CastaliaInstitute/luminary/assets/display-nubble-720x1280.png

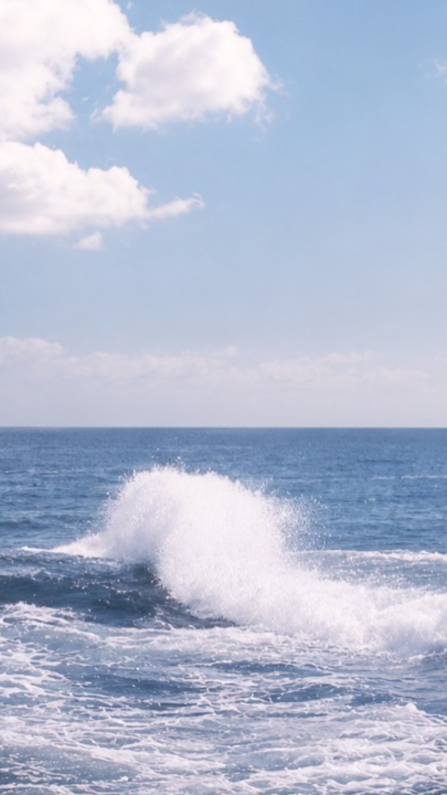
assets/display-nubble-720x1280.png
