CastaliaInstitute/luminary/assets/display-nubble-1024x600.png

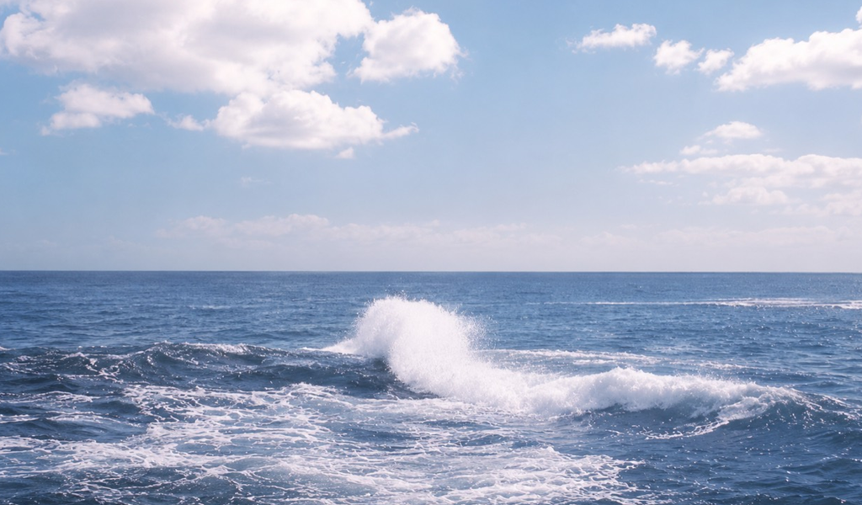
assets/display-nubble-1024x600.png
