CastaliaInstitute/luminary/assets/display-nubble-1131x720.png

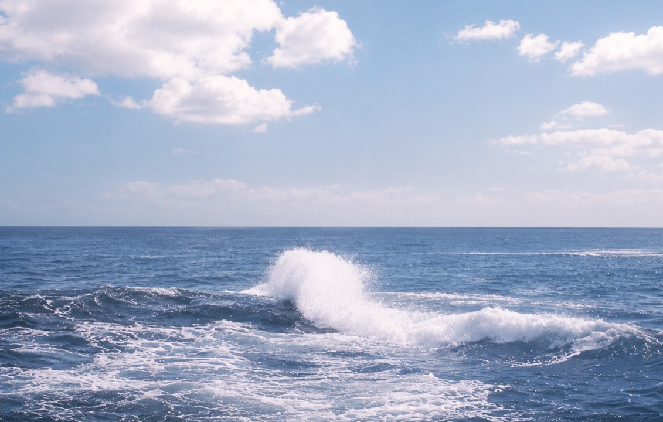
assets/display-nubble-1131x720.png
