CastaliaInstitute/luminary/assets/display-sky-sea-1280x720.png

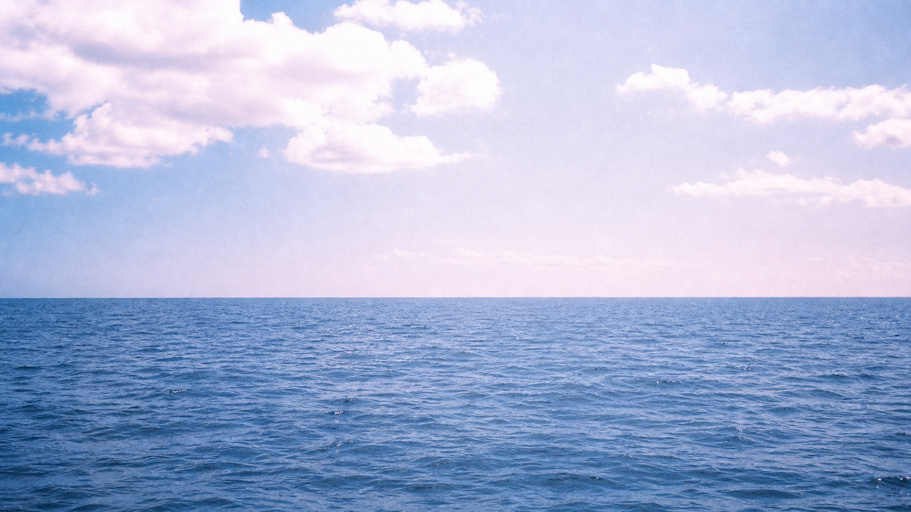
assets/display-sky-sea-1280x720.png
