CastaliaInstitute/luminary/assets/lighthouse-silhouette-reference-v2.png

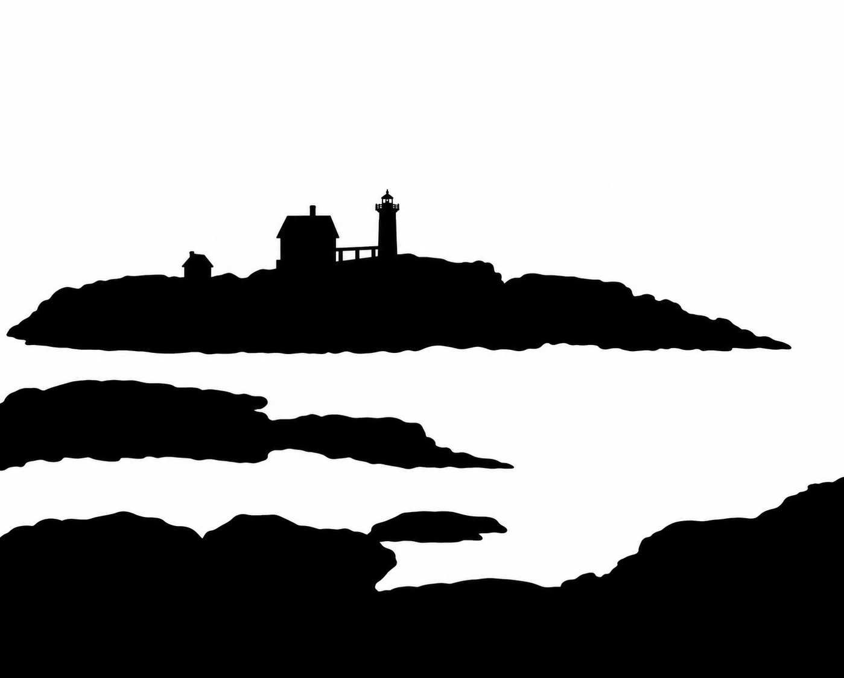
assets/lighthouse-silhouette-reference-v2.png
