CastaliaInstitute/luminary/assets/lighthouse-silhouette-source-v3.png

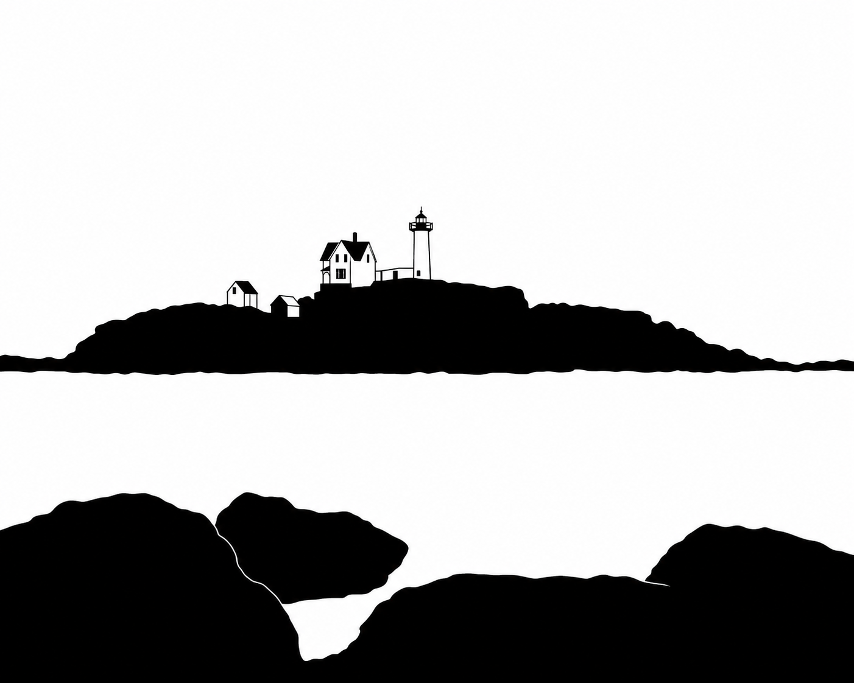
assets/lighthouse-silhouette-source-v3.png
