CastaliaInstitute/luminary/assets/source/nubble-background-ai.jpg

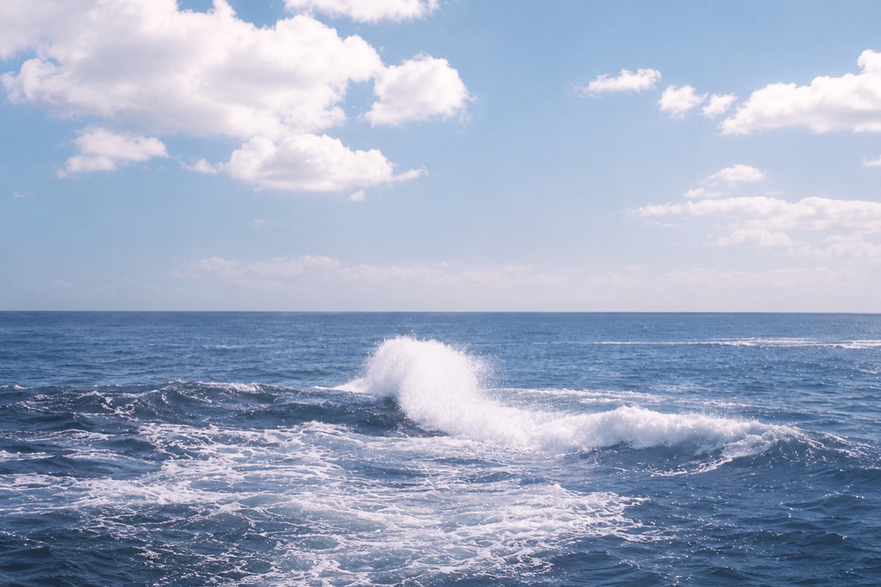
assets/source/nubble-background-ai.jpg
