CastaliaInstitute/luminary/assets/textures/distressed-white-reclaimed-wood-v1.png

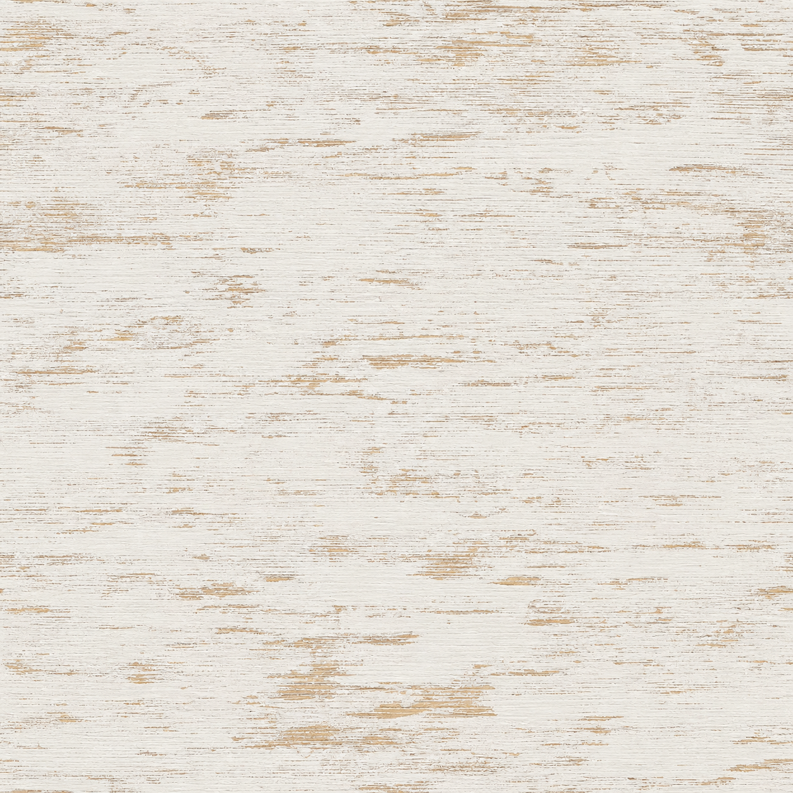
assets/textures/distressed-white-reclaimed-wood-v1.png
