CastaliaInstitute/luminary/firmware/luminary-background-viewer/assets/v2/nubble-sky-water-keyframe-v1.png

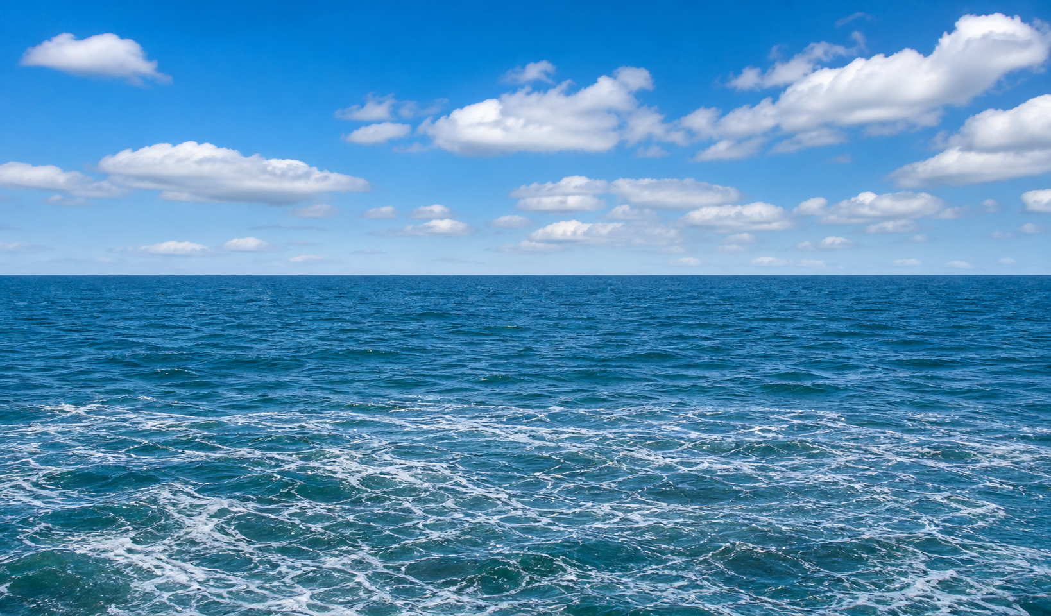
firmware/luminary-background-viewer/assets/v2/nubble-sky-water-keyframe-v1.png
