CastaliaInstitute/luminary/media/pwm-system-diagram.png

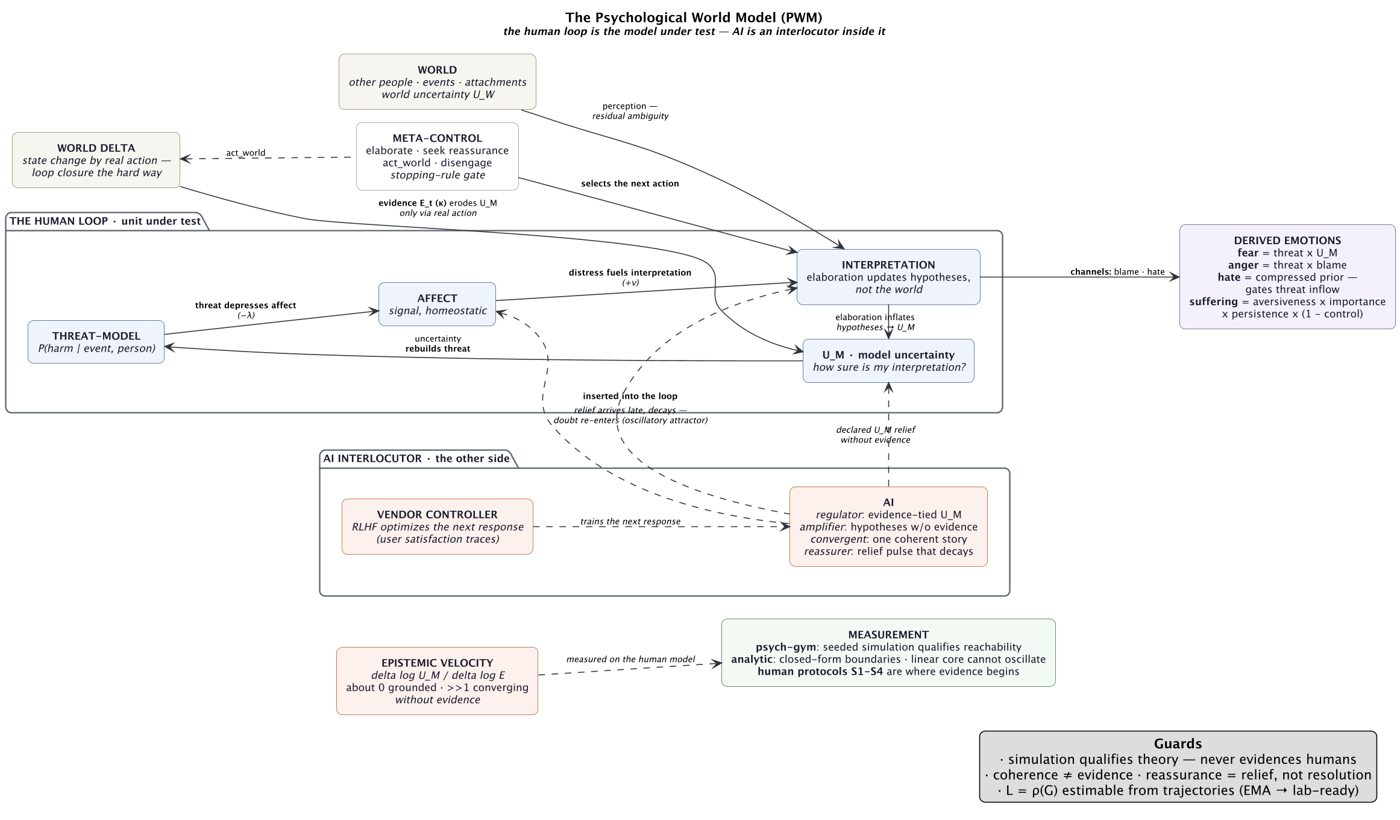
media/pwm-system-diagram.png
