CastaliaInstitute/luminary/references/Distressed White Frame.jpg

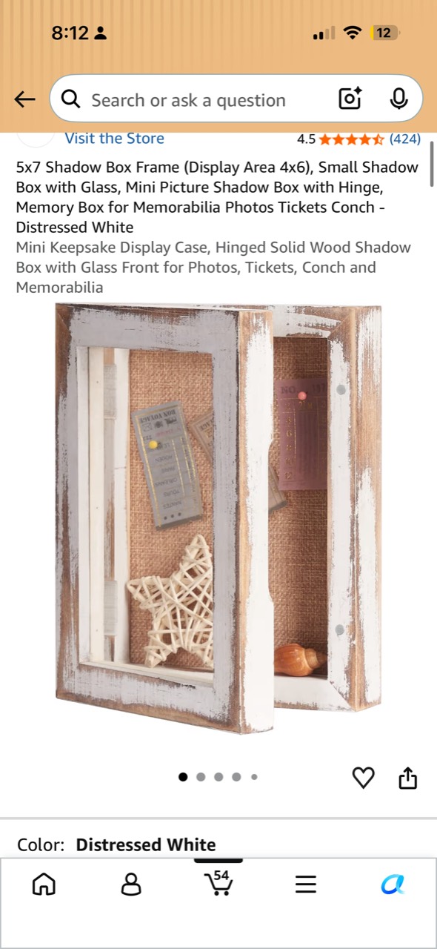
references/Distressed White Frame.jpg
