CastaliaInstitute/luminary/references/Pasted Image 1.jpg

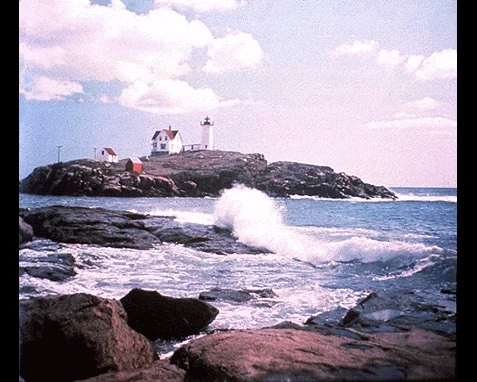
references/Pasted Image 1.jpg
