CastaliaInstitute/luminary/references/Photo 1.jpg

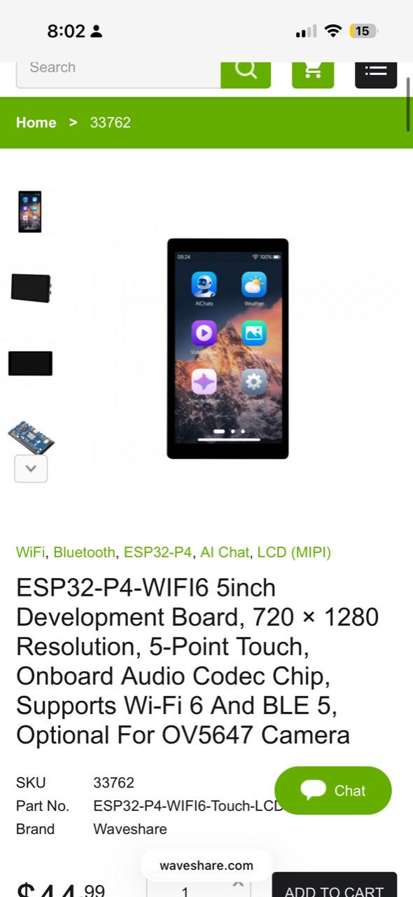
references/Photo 1.jpg
