CastaliaInstitute/luminary/references/Photo 2.jpg

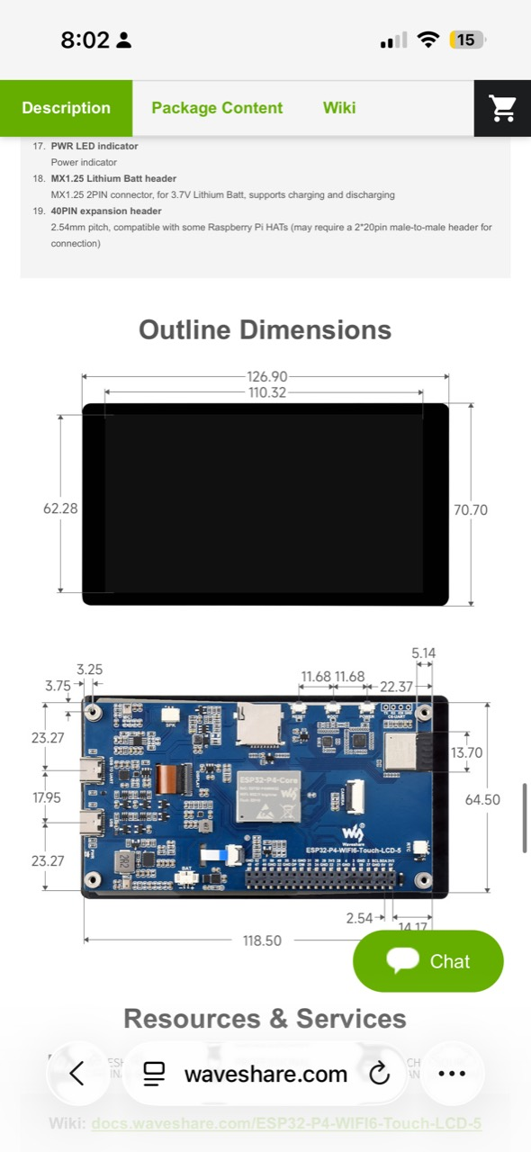
references/Photo 2.jpg
