CastaliaInstitute/luminary/scenes/nubble-aligned/background.png

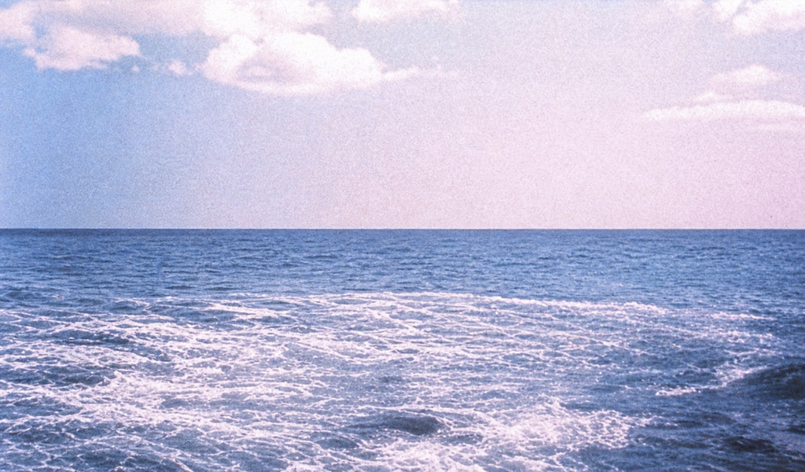
scenes/nubble-aligned/background.png
