CastaliaInstitute/luminary/scenes/nubble-aligned/breaker-source-sam2-review.png

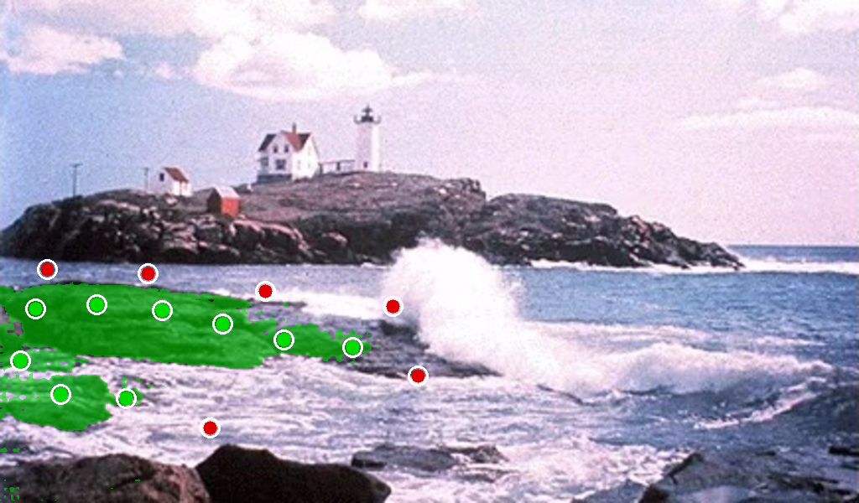
scenes/nubble-aligned/breaker-source-sam2-review.png
