CastaliaInstitute/luminary/scenes/nubble-aligned/breaker-source-segmentation.png

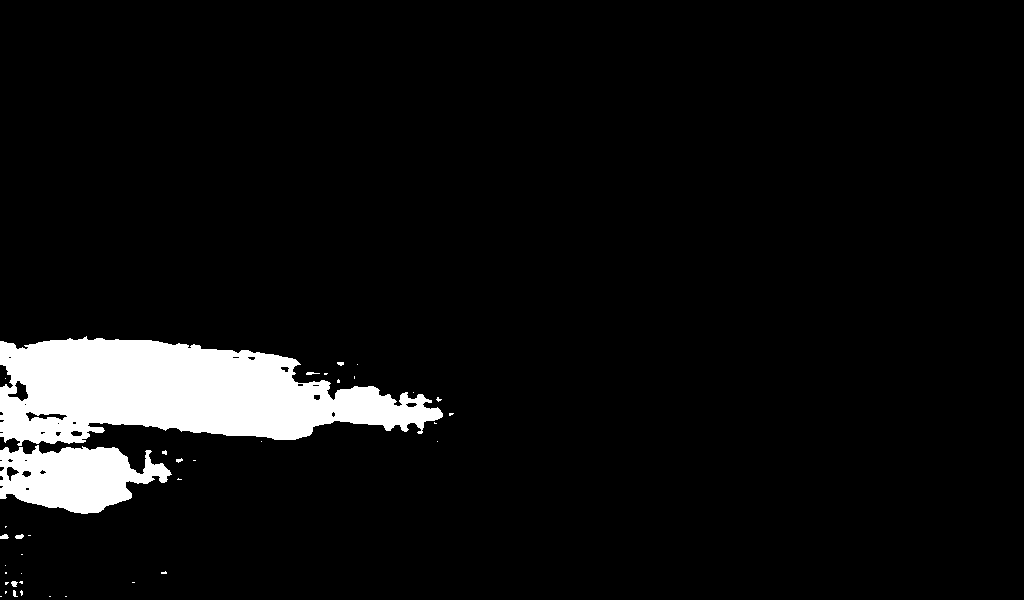
scenes/nubble-aligned/breaker-source-segmentation.png
