CastaliaInstitute/luminary/scenes/nubble-aligned/compiled/alignment-preview.png

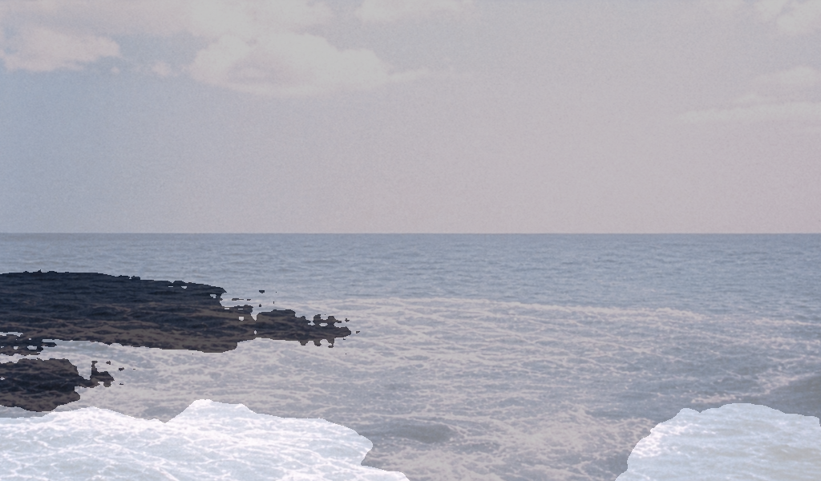
scenes/nubble-aligned/compiled/alignment-preview.png
