CastaliaInstitute/luminary/scenes/nubble-aligned/compiled/background-cropped.png

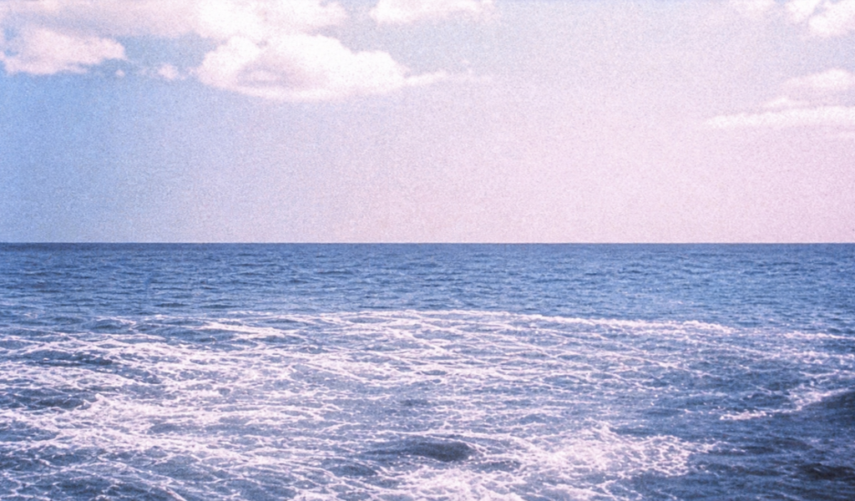
scenes/nubble-aligned/compiled/background-cropped.png
