CastaliaInstitute/luminary/scenes/nubble-aligned/compiled/breaker-mask.png

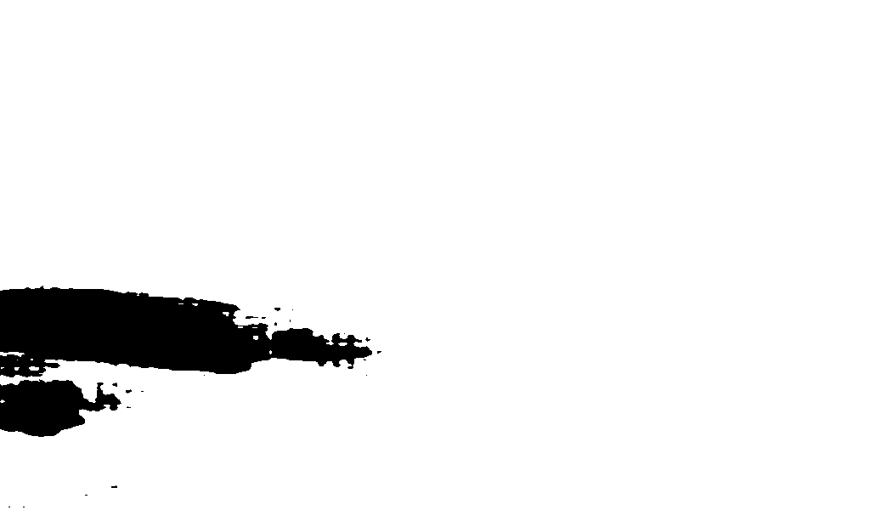
scenes/nubble-aligned/compiled/breaker-mask.png
