CastaliaInstitute/luminary/scenes/nubble-aligned/compiled/breaker-texture-45.png

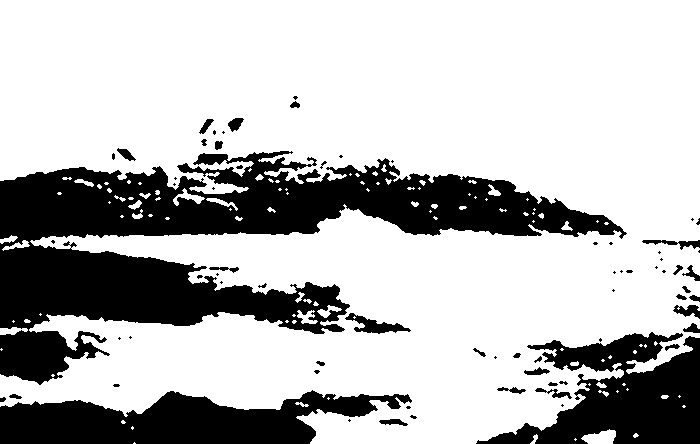
scenes/nubble-aligned/compiled/breaker-texture-45.png
