CastaliaInstitute/luminary/scenes/nubble-aligned/compiled/breaker-texture-65.png

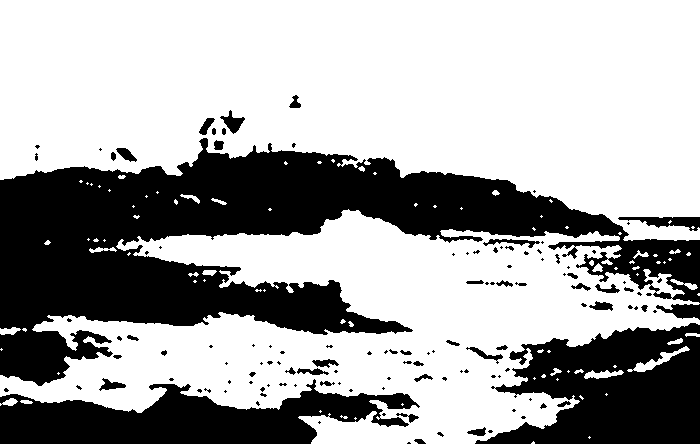
scenes/nubble-aligned/compiled/breaker-texture-65.png
