CastaliaInstitute/luminary/scenes/nubble-aligned/compiled/breaker-texture-82.png

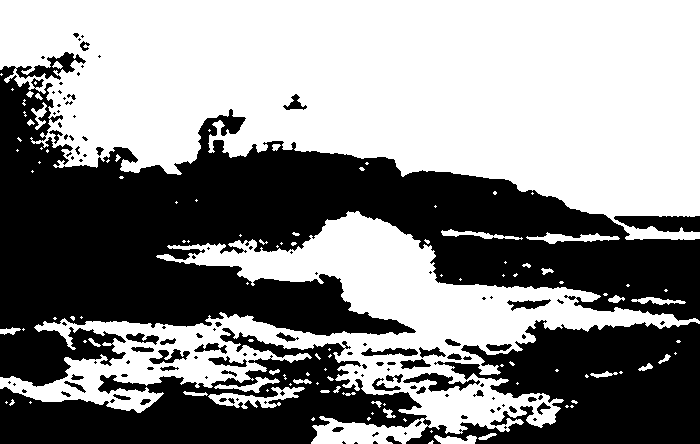
scenes/nubble-aligned/compiled/breaker-texture-82.png
