CastaliaInstitute/luminary/scenes/nubble-aligned/compiled/breaker-texture.png

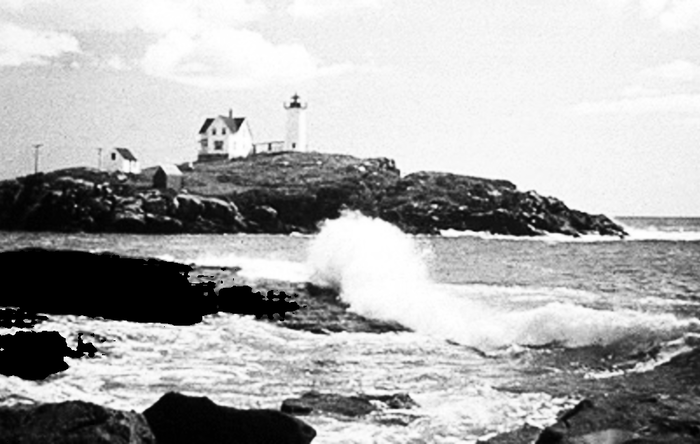
scenes/nubble-aligned/compiled/breaker-texture.png
