CastaliaInstitute/luminary/scenes/nubble-aligned/compiled/depth.png

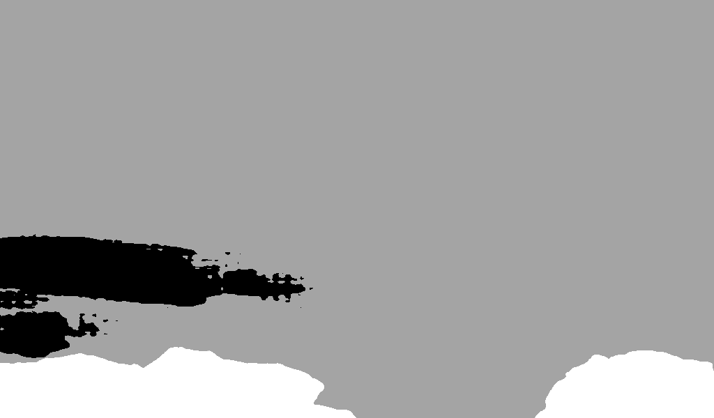
scenes/nubble-aligned/compiled/depth.png
