CastaliaInstitute/luminary/scenes/nubble-aligned/compiled/foreground-cropped.png

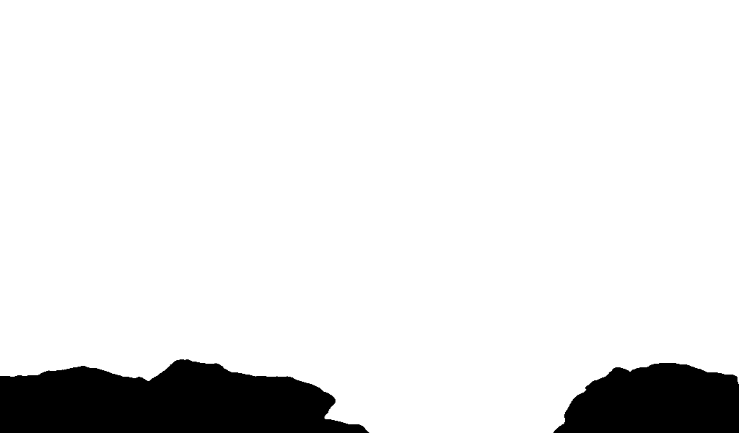
scenes/nubble-aligned/compiled/foreground-cropped.png
