CastaliaInstitute/luminary/scenes/nubble-aligned/compiled/foreground-mask.png

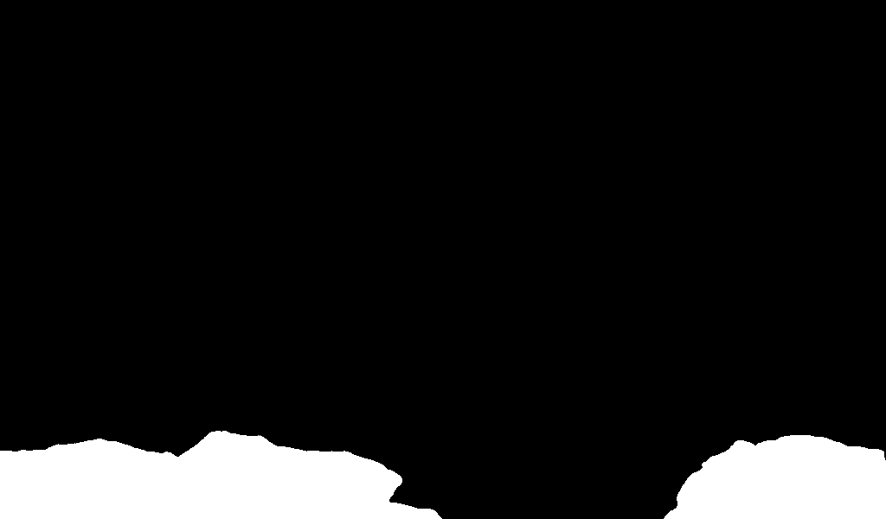
scenes/nubble-aligned/compiled/foreground-mask.png
