CastaliaInstitute/luminary/scenes/nubble-aligned/compiled/foreground-texture-45.png

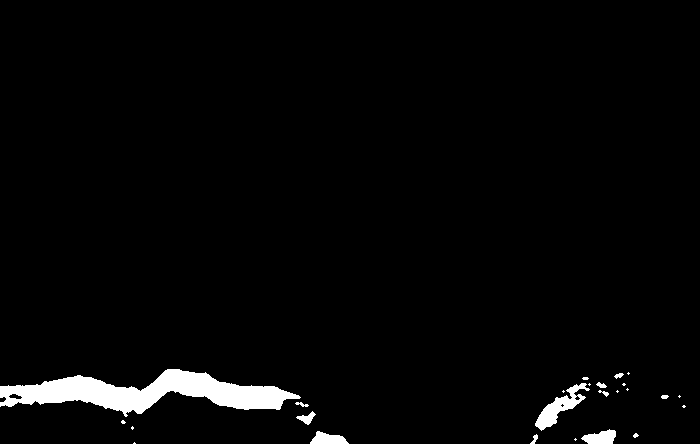
scenes/nubble-aligned/compiled/foreground-texture-45.png
