CastaliaInstitute/luminary/scenes/nubble-aligned/compiled/island-ai-separation.png

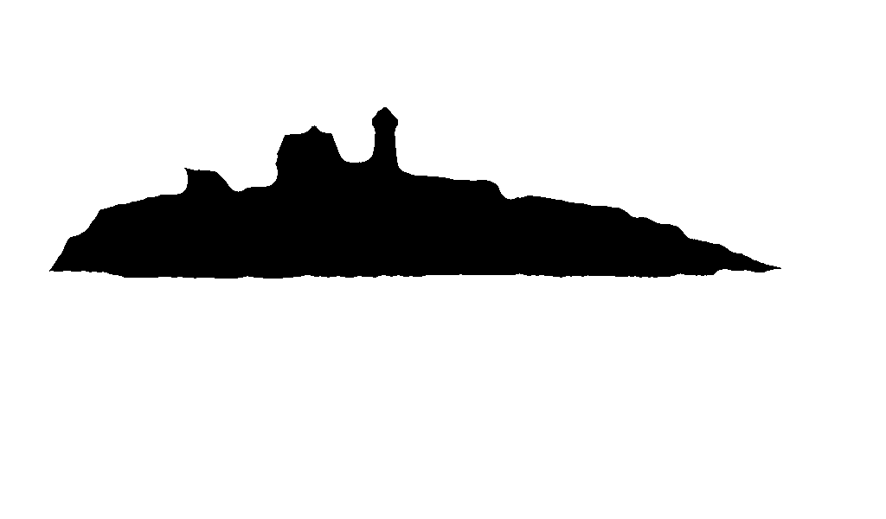
scenes/nubble-aligned/compiled/island-ai-separation.png
