CastaliaInstitute/luminary/scenes/nubble-aligned/compiled/island-texture-45.png

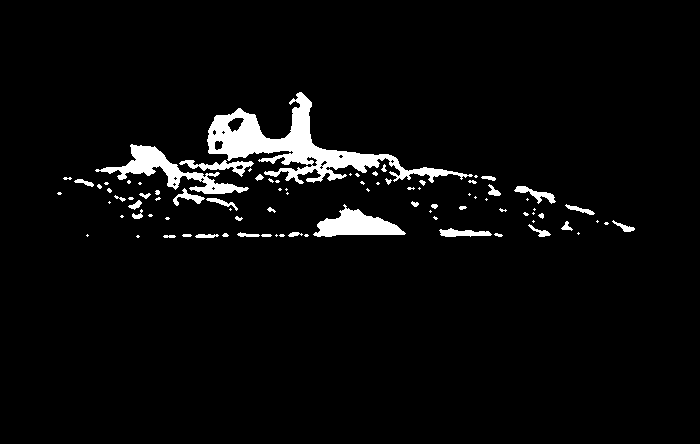
scenes/nubble-aligned/compiled/island-texture-45.png
