CastaliaInstitute/luminary/scenes/nubble-aligned/compiled/nubble-c85-plainsky.png

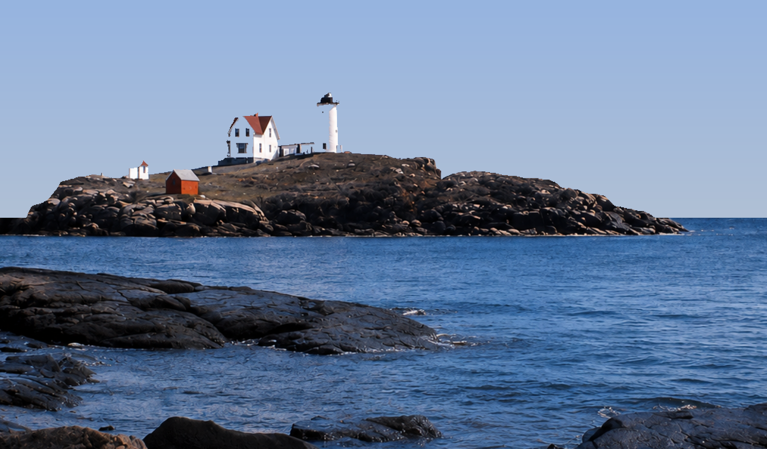
scenes/nubble-aligned/compiled/nubble-c85-plainsky.png
