CastaliaInstitute/luminary/scenes/nubble-aligned/compiled/nubble-c85-registered.png

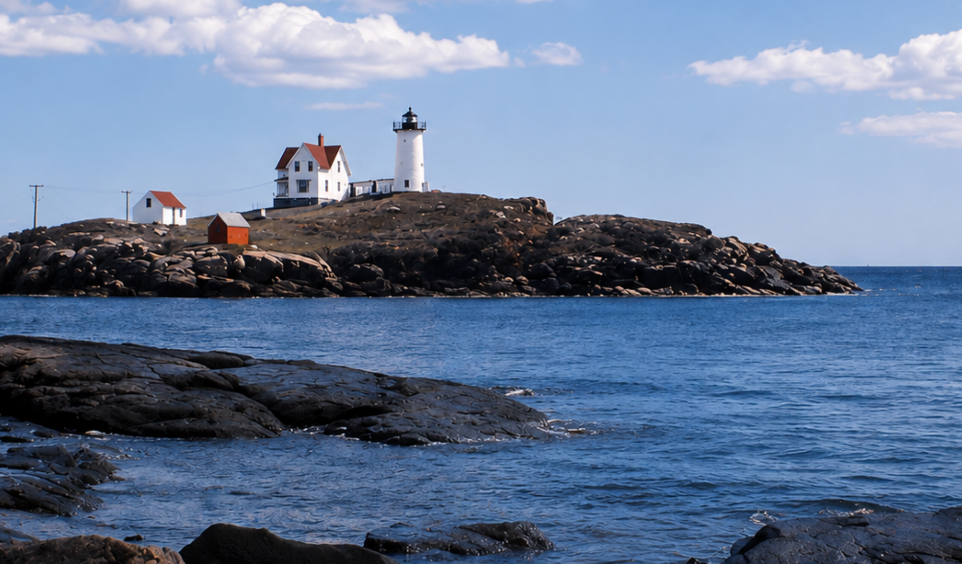
scenes/nubble-aligned/compiled/nubble-c85-registered.png
