CastaliaInstitute/luminary/scenes/nubble-aligned/compiled/ocean-map-preview.png

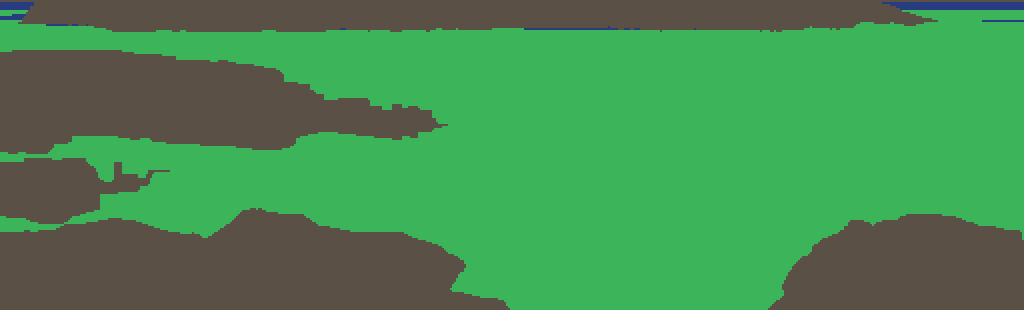
scenes/nubble-aligned/compiled/ocean-map-preview.png
