CastaliaInstitute/luminary/scenes/nubble-aligned/compiled/rock-detail.png

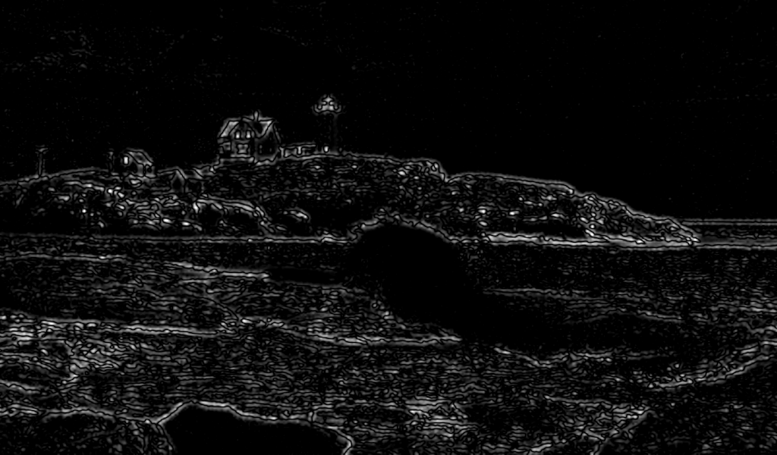
scenes/nubble-aligned/compiled/rock-detail.png
