CastaliaInstitute/luminary/scenes/nubble-aligned/compiled/source-cropped.png

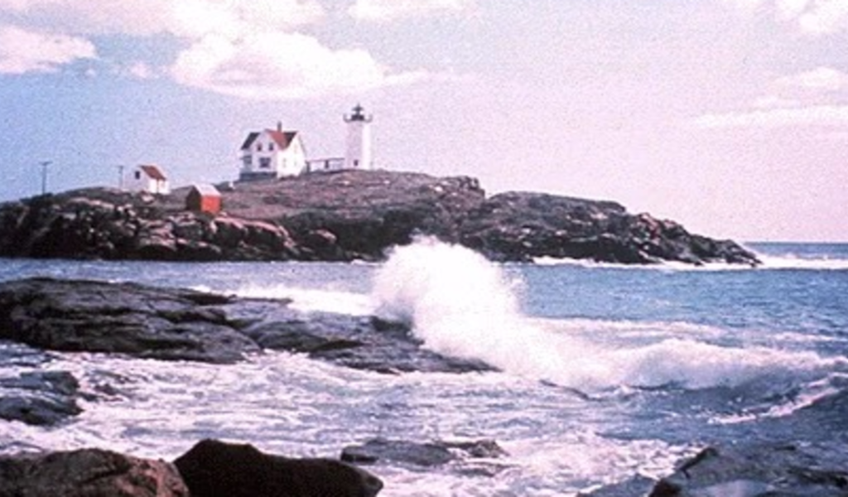
scenes/nubble-aligned/compiled/source-cropped.png
