CastaliaInstitute/luminary/scenes/nubble-aligned/foreground.png

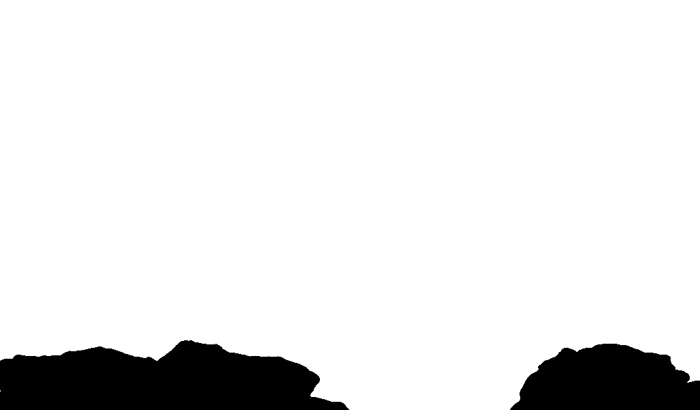
scenes/nubble-aligned/foreground.png
