CastaliaInstitute/luminary/scenes/nubble-aligned/island-ai-separation.jpg

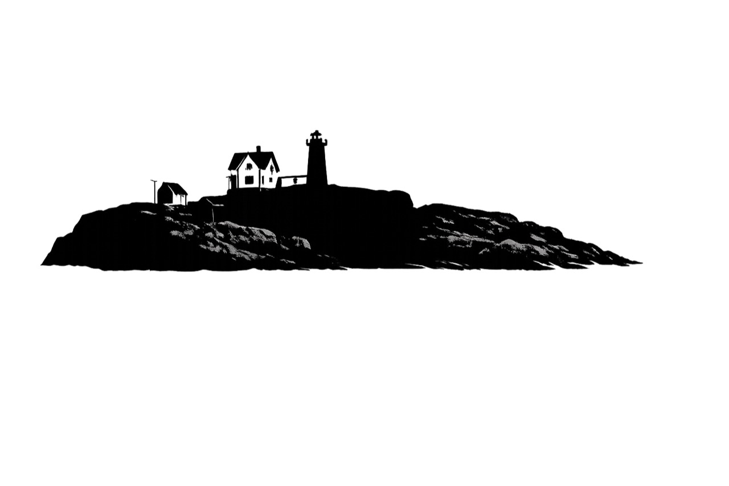
scenes/nubble-aligned/island-ai-separation.jpg
