CastaliaInstitute/luminary/scenes/nubble-aligned/island.png

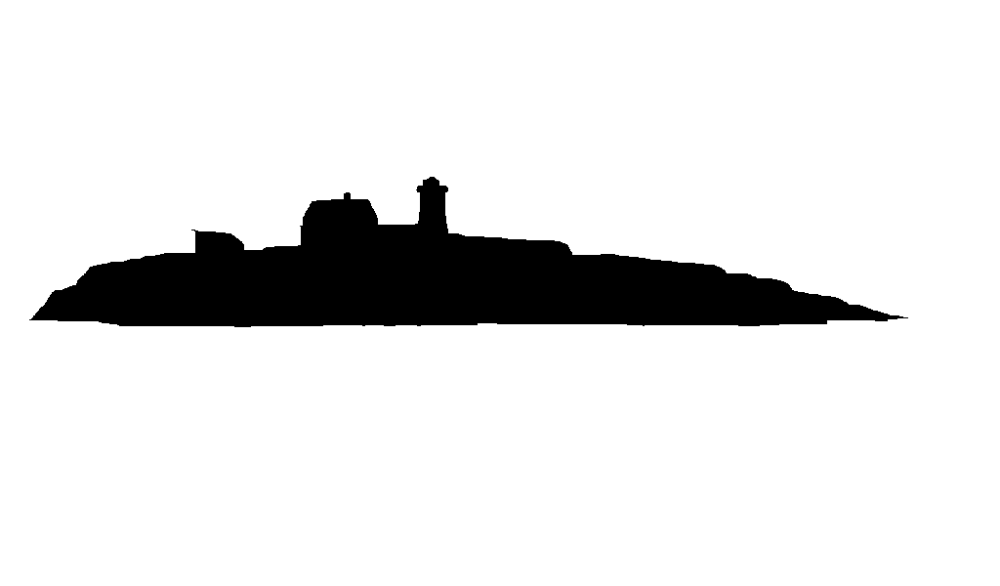
scenes/nubble-aligned/island.png
