CastaliaInstitute/luminary/scenes/nubble/breaker.png

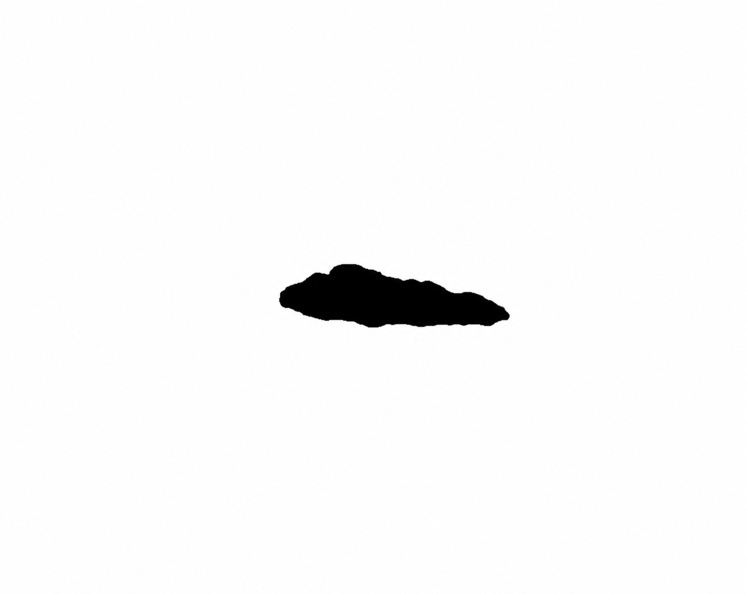
scenes/nubble/breaker.png
