CastaliaInstitute/luminary/scenes/nubble/compiled/alignment-preview.png

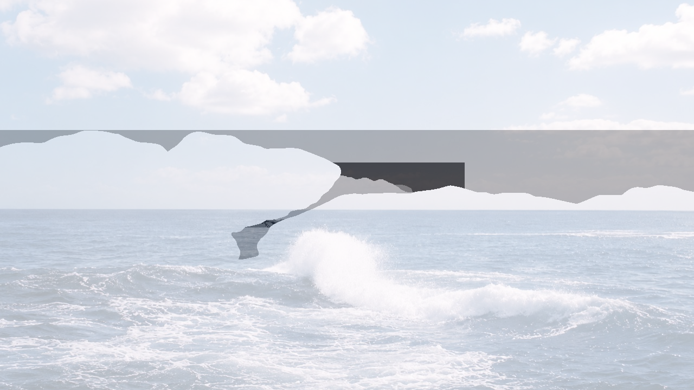
scenes/nubble/compiled/alignment-preview.png
