CastaliaInstitute/luminary/scenes/nubble/compiled/depth.png

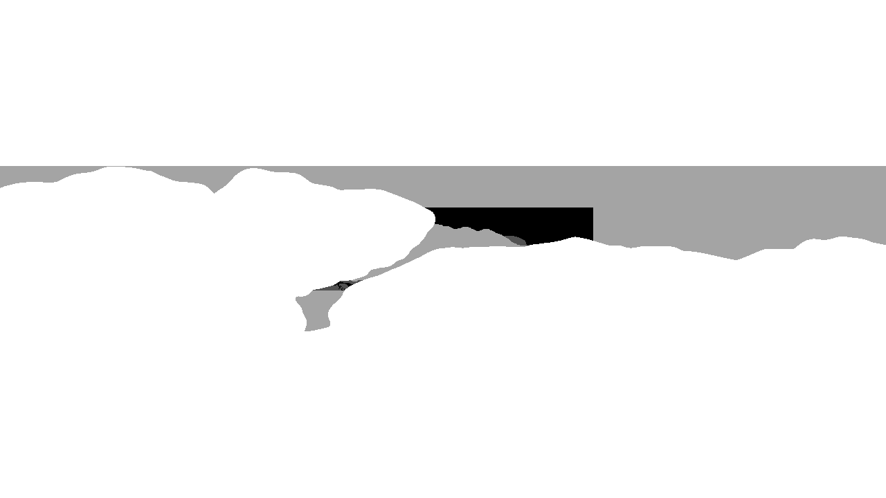
scenes/nubble/compiled/depth.png
