CastaliaInstitute/luminary/scenes/nubble/compiled/island-mask.png

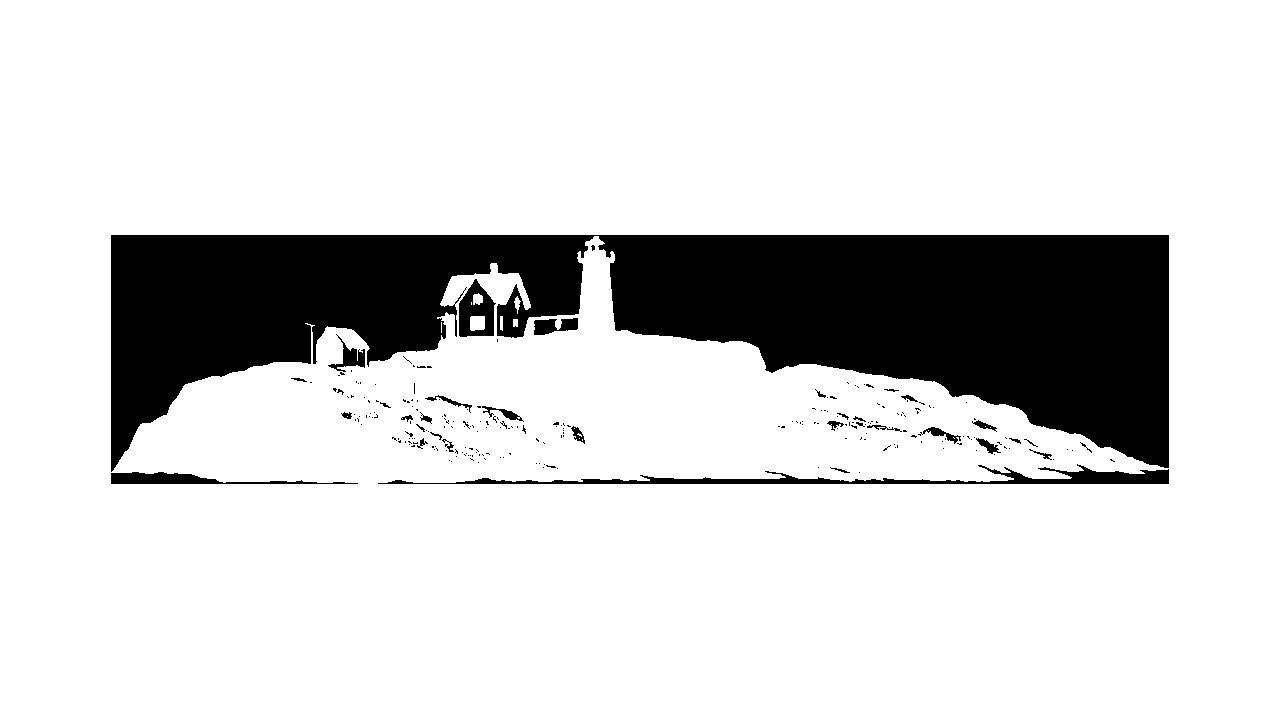
scenes/nubble/compiled/island-mask.png
