CastaliaInstitute/luminary/scenes/nubble/foreground.png

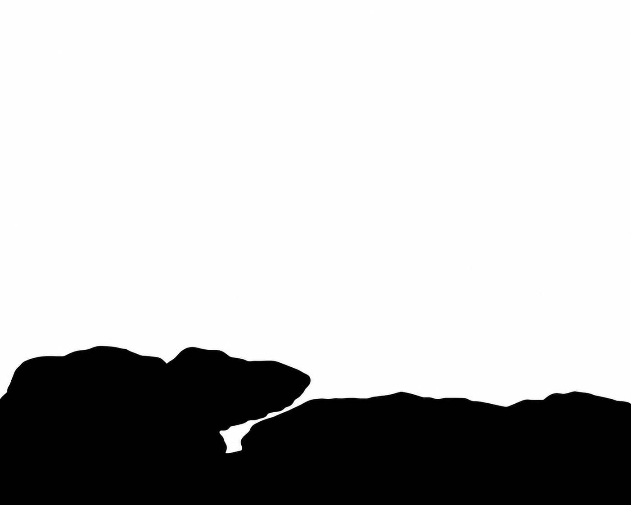
scenes/nubble/foreground.png
