CastaliaInstitute/luminary/site/cliffhouse/assets/cliff-house-foreground.png

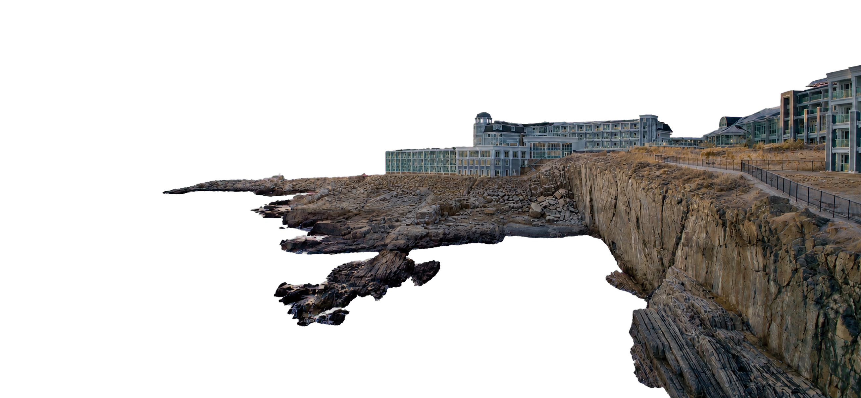
site/cliffhouse/assets/cliff-house-foreground.png
