CastaliaInstitute/luminary/site/cliffhouse/assets/cliff-house-land-mask.png

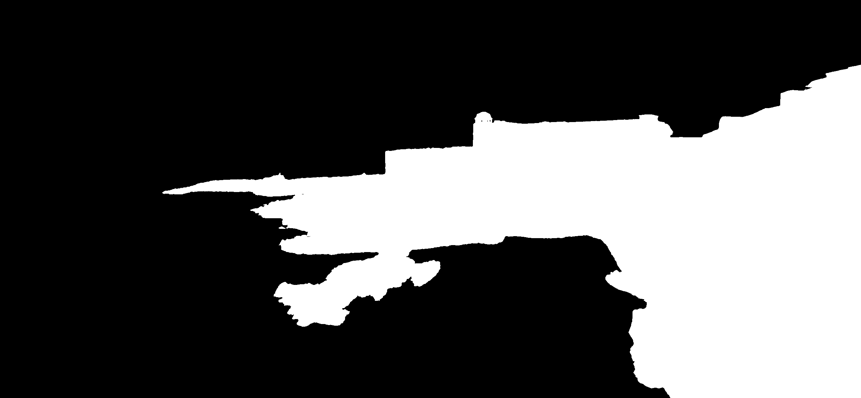
site/cliffhouse/assets/cliff-house-land-mask.png
