CastaliaInstitute/luminary/site/cliffhouse/assets/cliff-house-ocean-texture.jpg

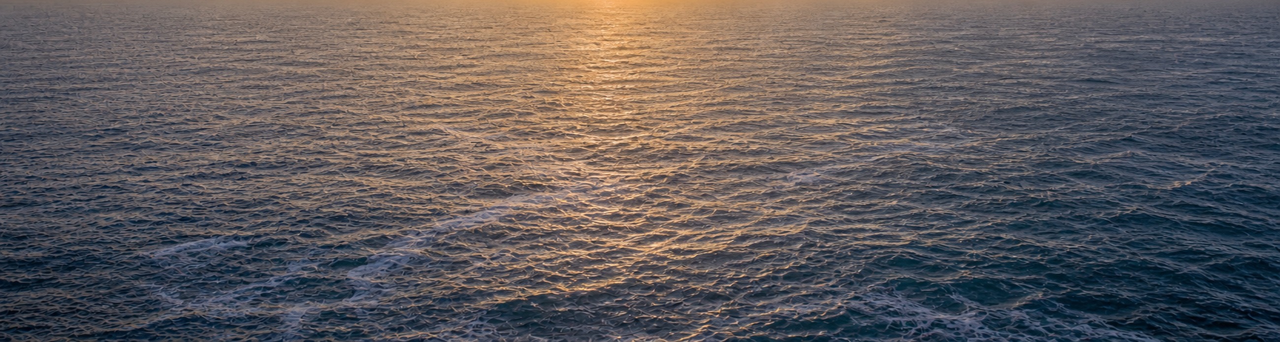
site/cliffhouse/assets/cliff-house-ocean-texture.jpg
