CastaliaInstitute/luminary/site/cliffhouse/assets/cliff-house-shore-mask.png

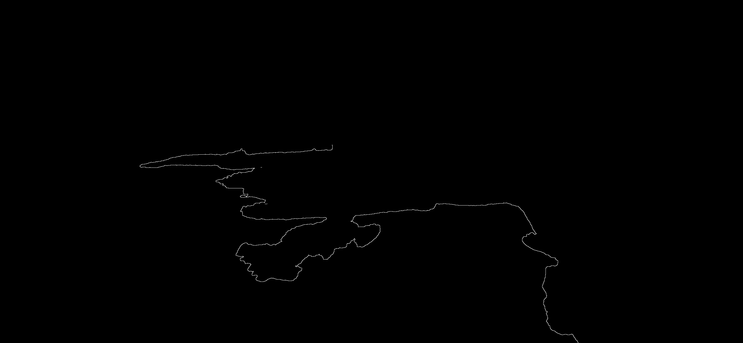
site/cliffhouse/assets/cliff-house-shore-mask.png
