CastaliaInstitute/luminary/site/cliffhouse/runtime/clouds/cloud-frame-000.png

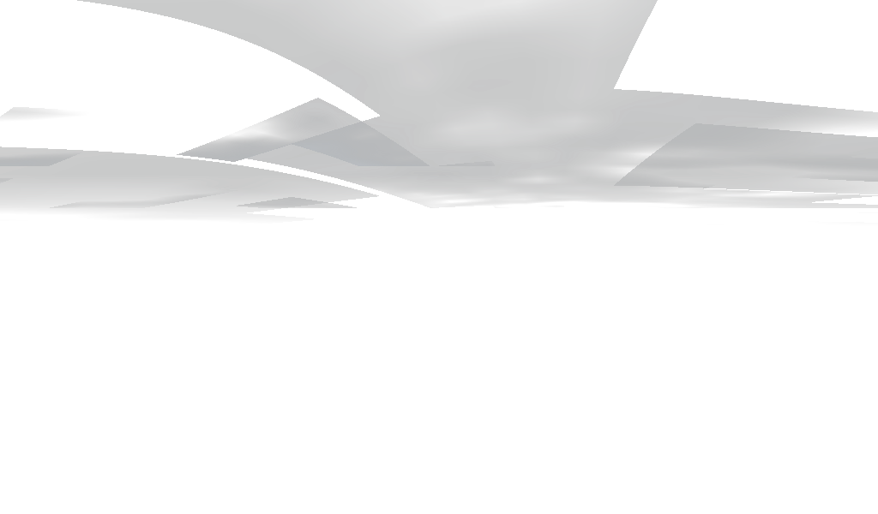
site/cliffhouse/runtime/clouds/cloud-frame-000.png
