CastaliaInstitute/luminary/site/nubble/nubble-island.png

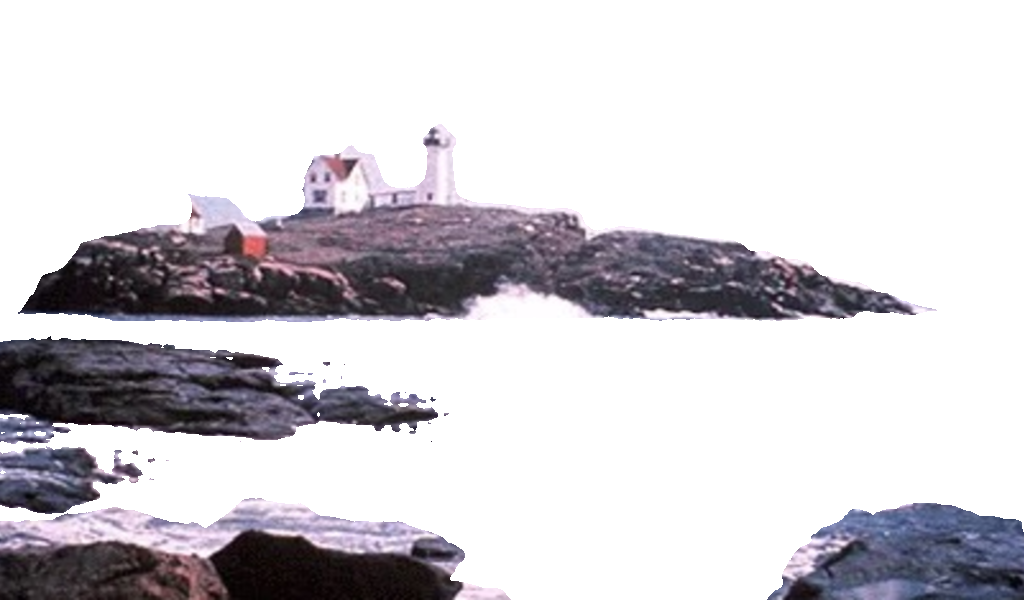
site/nubble/nubble-island.png
