CastaliaInstitute/luminary/site/nubble/nubble-ocean-2x.jpg

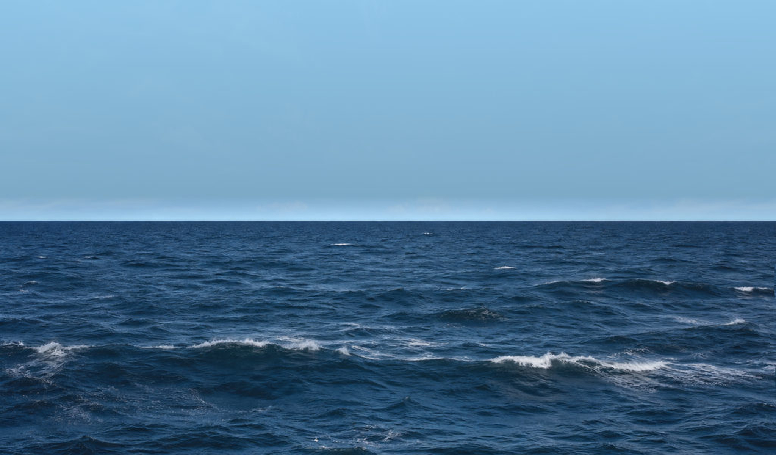
site/nubble/nubble-ocean-2x.jpg
