CastaliaInstitute/luminary/tools/ocean-sim/nubble_depth_preview.png

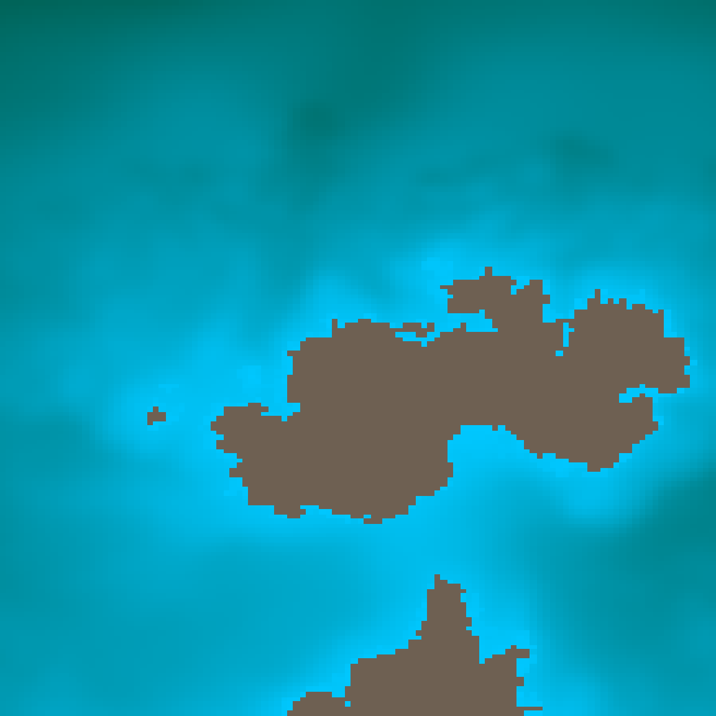
tools/ocean-sim/nubble_depth_preview.png
