CastaliaInstitute/luminary/renders/stl/nubble-basrelief-breaker.stl

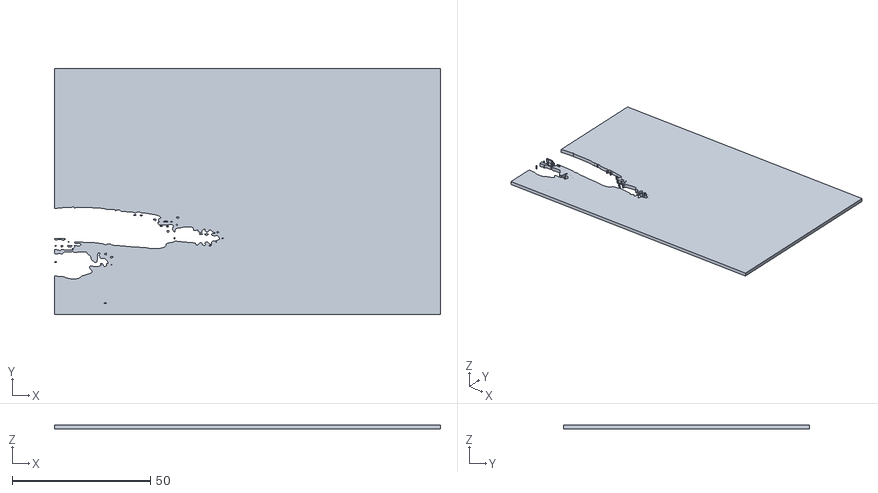
[picture p72: CAD file, 2026-07-27]
renders/stl/nubble-basrelief-breaker.stl
139.7 x 88.9 x 1.60
