CastaliaInstitute/luminary/renders/stl/nubble-foreground-layer.stl

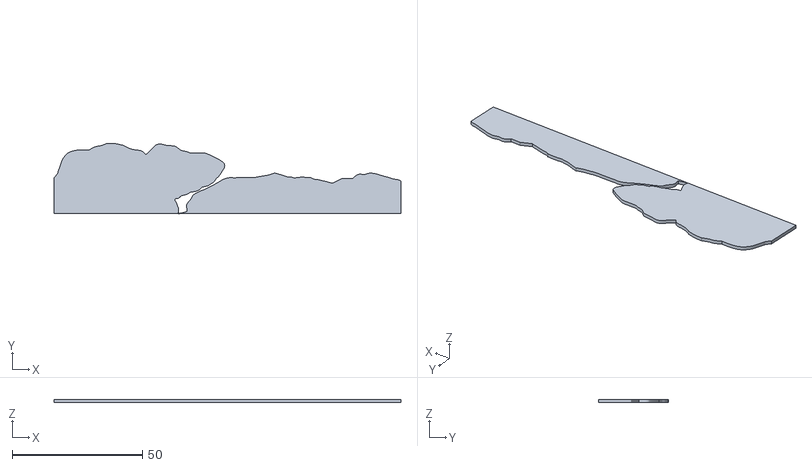
[picture p73: CAD file, 2026-07-27]
renders/stl/nubble-foreground-layer.stl
133.0 x 27.0 x 1.20
