CastaliaInstitute/luminary/renders/stl/luminary-7in-p4-backplate.stl

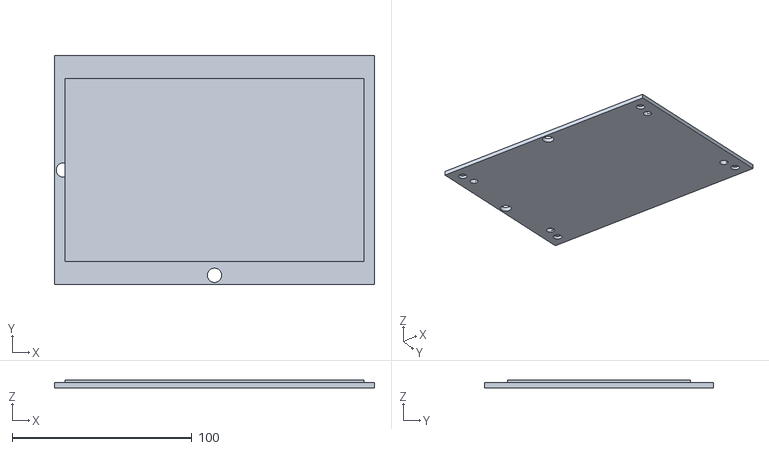
[picture p74: CAD file, 2026-07-26]
renders/stl/luminary-7in-p4-backplate.stl
177.8 x 127.0 x 4.19
