CastaliaInstitute/luminary/renders/stl/luminary-7in-p4-fit-check.stl

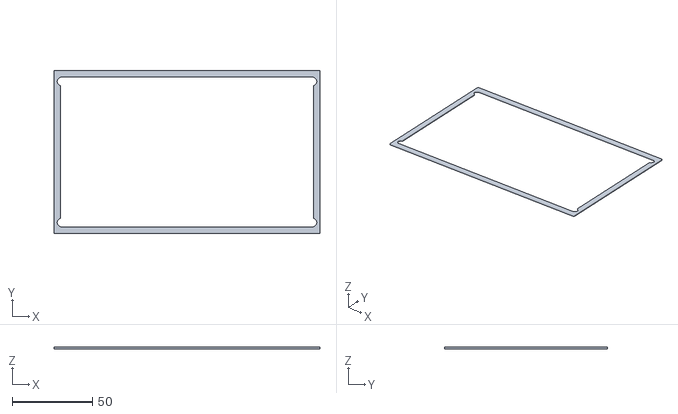
[picture p75: CAD file, 2026-07-26]
renders/stl/luminary-7in-p4-fit-check.stl
166.0 x 101.6 x 1.00
