CastaliaInstitute/luminary/renders/stl/luminary-structures.stl

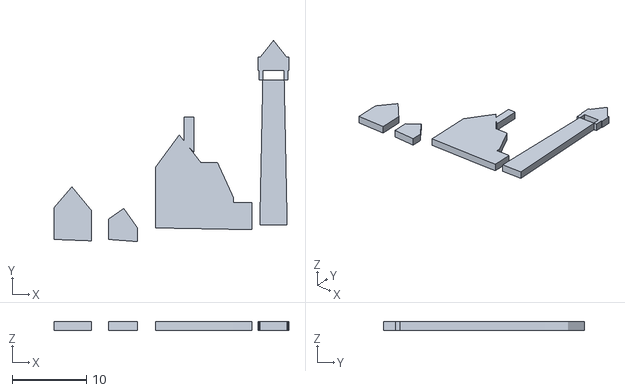
[picture p76: CAD file, 2026-07-26]
renders/stl/luminary-structures.stl
31.6 x 27.1 x 1.20
