CastaliaInstitute/luminary/renders/stl/luminary-silhouette.stl

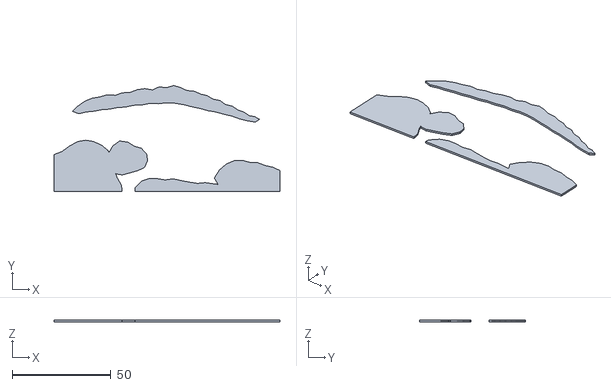
[picture p77: CAD file, 2026-07-26]
renders/stl/luminary-silhouette.stl
114.3 x 53.6 x 0.8
