CastaliaInstitute/luminary/renders/stl/luminary-display-carrier.stl

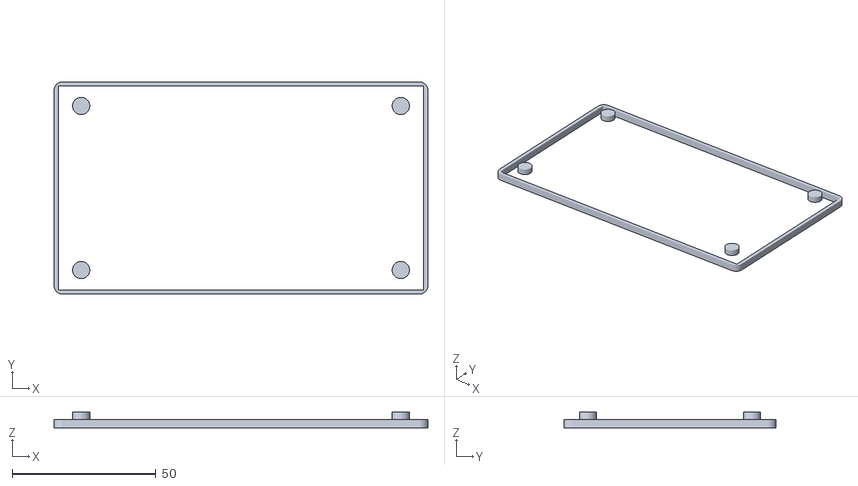
[picture p78: CAD file, 2026-07-26]
renders/stl/luminary-display-carrier.stl
129.9 x 73.7 x 5.50
