CastaliaInstitute/luminary/renders/stl/luminary-silhouette-carrier.stl

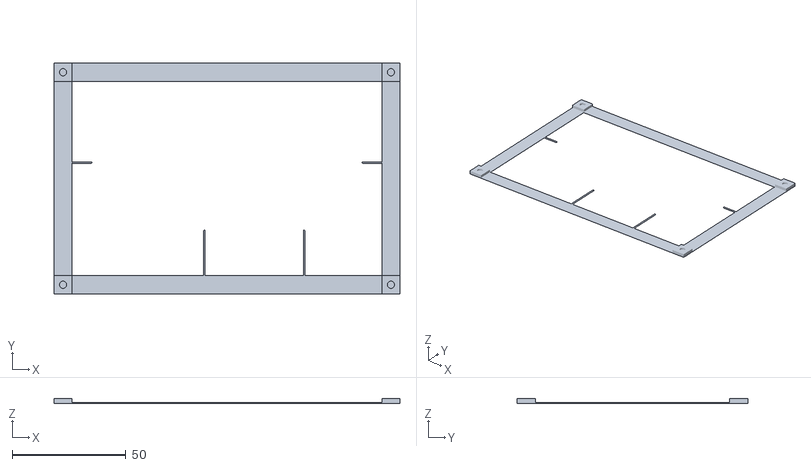
[picture p79: CAD file, 2026-07-26]
renders/stl/luminary-silhouette-carrier.stl
152.4 x 101.6 x 2.00
