CastaliaInstitute/luminary/renders/stl/luminary-backplate.stl

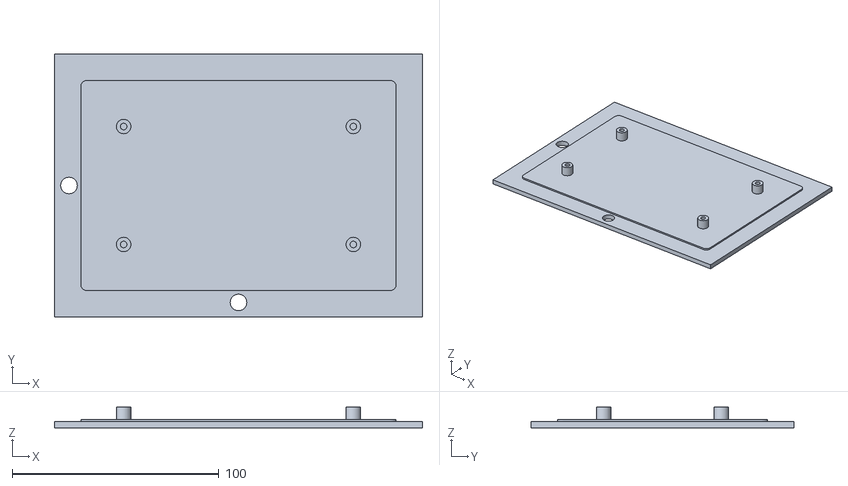
[picture p80: CAD file, 2026-07-26]
renders/stl/luminary-backplate.stl
177.8 x 127.0 x 10.0
