CastaliaInstitute/luminary/renders/nubble-concept-rear-assembly.png

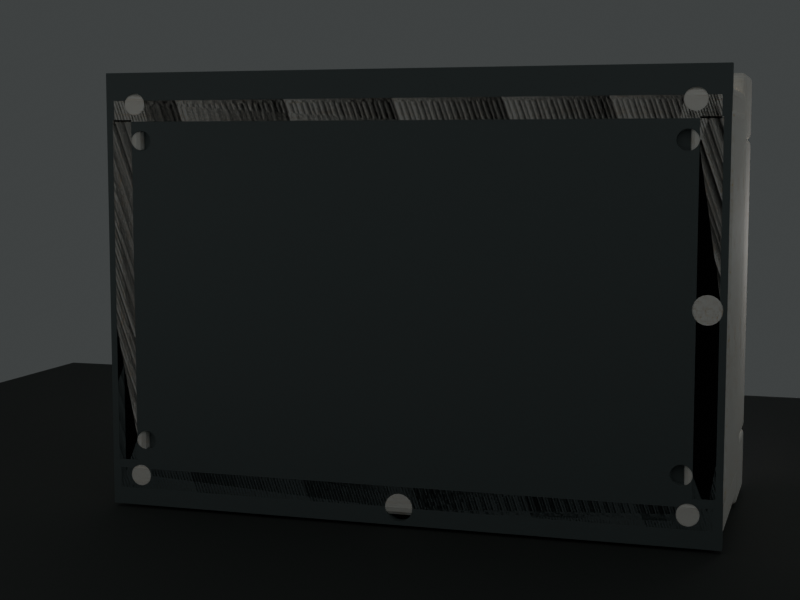
renders/nubble-concept-rear-assembly.png
