CastaliaInstitute/luminary/site/cliffhouse/assets/cliff-house-buildings-mask.png

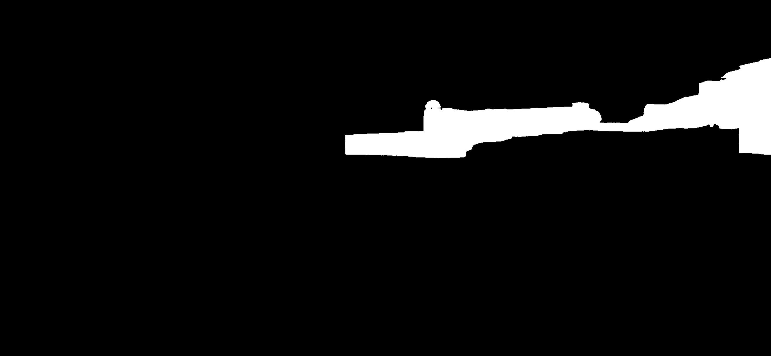
site/cliffhouse/assets/cliff-house-buildings-mask.png
